CoCoSprite629/Aurora/ESP32_Project/include/dataTransmit.h

#ifndef DATATRANSMIT_H_
#define DATATRANSMIT_H_

extern String temperature;
void get_ADcode();
void getTodayWeather();
void todayWeatherTransmit();
void getFutureWeather();
void futureWeatherTransmit();
void getFestival();
void festivalTransmit();
void setTime();
void setTimeTransmit();

#endif
